jax-b/ModulerKTNE/Planing_Drawings/FrontOfDevice.JPG

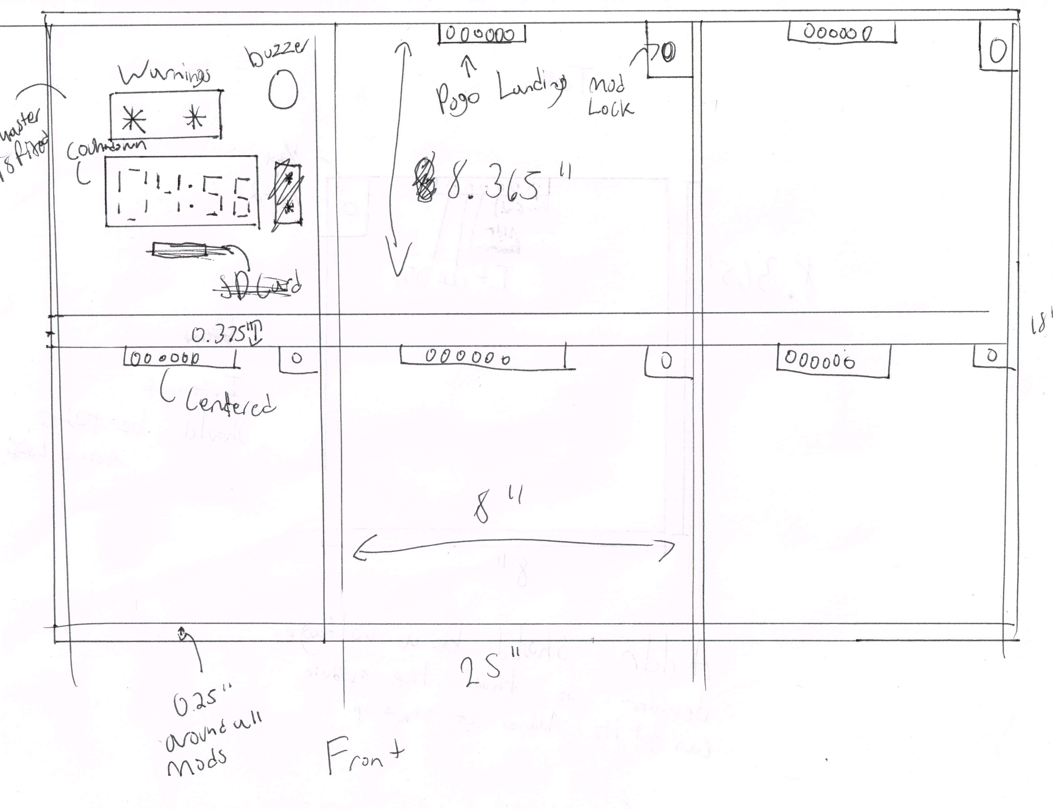
Planing_Drawings/FrontOfDevice.JPG
