jax-b/ModulerKTNE/Planing_Drawings/ModAddrs.JPG

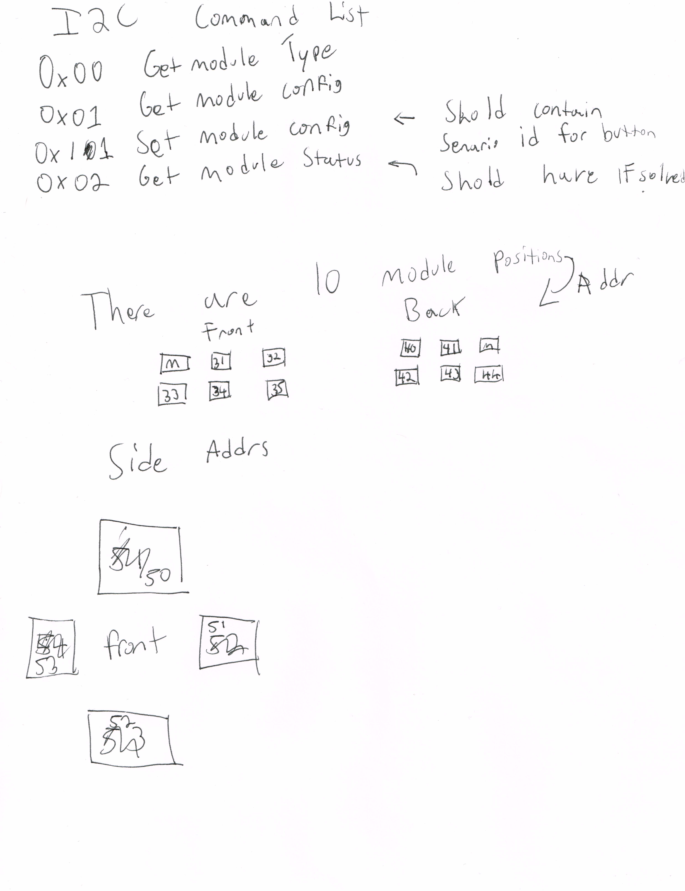
Planing_Drawings/ModAddrs.JPG
