jax-b/ModulerKTNE/Planing_Drawings/TheButton.JPG

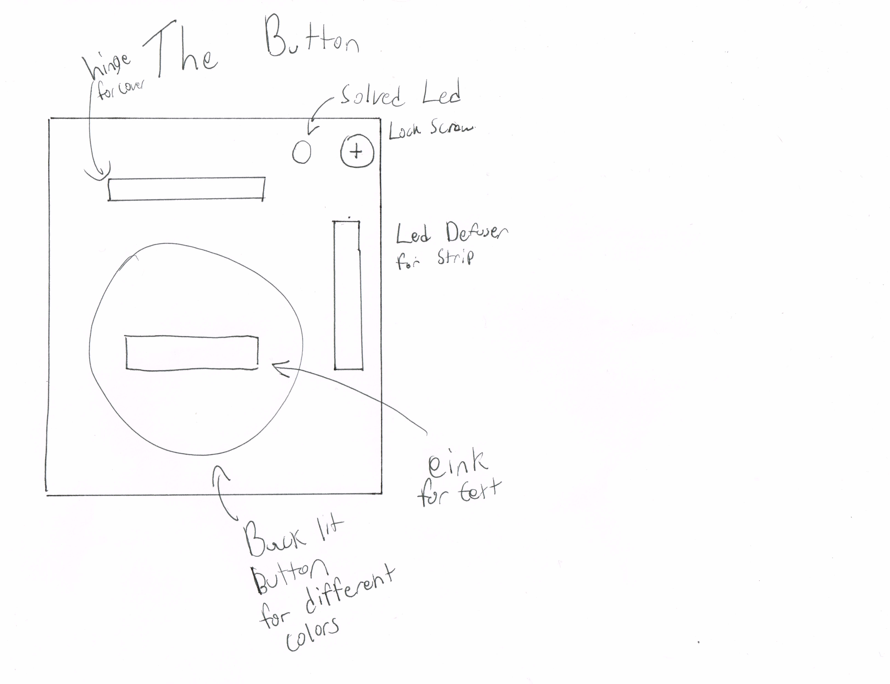
Planing_Drawings/TheButton.JPG
