jax-b/ModulerKTNE/SidePanel/Artwork/D.jpg

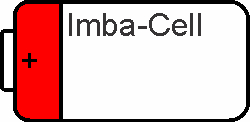
SidePanel/Artwork/D.jpg
