jax-b/ModulerKTNE/Modules/src/OTS_Wires/OTS_Wires Cut Buttons.3mf

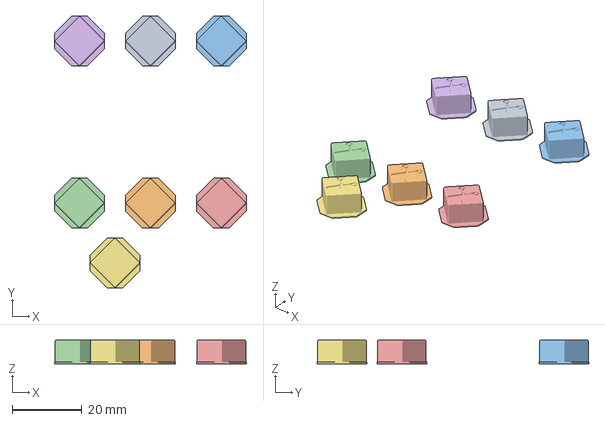
[picture p32: CAD file, 2022-03-22]
Modules/src/OTS_Wires/OTS_Wires Cut Buttons.3mf
55.1 x 78.1 x 6.86 mm
