jax-b/ModulerKTNE/SidePanel/LeftSideConductor/src/PortPictures.h

// Total bytes used to store images in PROGMEM = 6928
// 'rj45', 56x61px
const uint16_t epd_bitmap_rj45_size [] PROGMEM = { 56, 61 };
const unsigned char epd_bitmap_rj45_Black [] PROGMEM = {
	0x00, 0x00, 0x00, 0x00, 0x00, 0x00, 0x00, 0x7f, 0xff, 0xff, 0xff, 0xff, 0xff, 0xfe, 0x7f, 0xff, 
	0xff, 0xff, 0xff, 0xff, 0xfe, 0x7f, 0xff, 0xff, 0xff, 0xff, 0xff, 0xfe, 0x7f, 0xff, 0xff, 0xff, 
	0xff, 0xff, 0xfe, 0x7f, 0xff, 0xff, 0xff, 0xff, 0xff, 0xfe, 0x7f, 0xff, 0xff, 0xff, 0xff, 0xff, 
	0xfe, 0x7f, 0xff, 0xff, 0xff, 0xff, 0xff, 0xfe, 0x7f, 0xff, 0xff, 0xff, 0xff, 0xff, 0xfe, 0x7f, 
	0x00, 0x00, 0x00, 0x00, 0x00, 0x7e, 0x7f, 0x00, 0x00, 0x00, 0x00, 0x00, 0x7e, 0x7f, 0x00, 0x00, 
	0x00, 0x00, 0x00, 0x7e, 0x7f, 0x00, 0x00, 0x00, 0x00, 0x00, 0x7e, 0x7f, 0x00, 0x00, 0x00, 0x00, 
	0x00, 0x7e, 0x7f, 0x00, 0x00, 0x00, 0x00, 0x00, 0x7e, 0x7f, 0x00, 0x00, 0x00, 0x00, 0x00, 0x7e, 
	0x7f, 0x00, 0x00, 0x00, 0x00, 0x00, 0x7e, 0x7f, 0x00, 0x00, 0x00, 0x00, 0x00, 0x7e, 0x7f, 0x00, 
	0x00, 0x00, 0x00, 0x00, 0x7e, 0x7f, 0x00, 0x00, 0x00, 0x00, 0x00, 0x7e, 0x7f, 0x00, 0x00, 0x00, 
	0x00, 0x00, 0x7e, 0x7f, 0x00, 0x00, 0x00, 0x00, 0x00, 0x7e, 0x7f, 0x00, 0x00, 0x00, 0x00, 0x00, 
	0x7e, 0x7f, 0x00, 0x00, 0x00, 0x00, 0x00, 0x7e, 0x7f, 0x00, 0x00, 0x00, 0x00, 0x00, 0x7e, 0x7f, 
	0x00, 0x00, 0x00, 0x00, 0x00, 0x7e, 0x7f, 0x00, 0x00, 0x00, 0x00, 0x00, 0x7e, 0x7f, 0x00, 0x00, 
	0x00, 0x00, 0x00, 0x7e, 0x7f, 0x00, 0x00, 0x00, 0x00, 0x00, 0x7e, 0x7f, 0x00, 0x00, 0x00, 0x00, 
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
	0x01, 0xe0, 0x1e, 0x01, 0xe0, 0x1e, 0x1e, 0x1f, 0xff, 0xc0, 0x00, 0x3f, 0xe1, 0xc7, 0xff, 0x00, 
	0x1f, 0xfc, 0x78, 0x7f, 0xe3, 0xf0, 0x3f, 0x03, 0xf0, 0x3f, 0x03, 0xf0, 0x3f, 0x03, 0xf0, 0x3f, 
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
};
