jax-b/ModulerKTNE/Modules/src/OTS_Button/OTS_Button.h

#include "../baseModule/baseModule.h"
#include <Adafruit_NeoPixel.h>
#include <GxEPD2_BW.h>
#include <Fonts/FreeMonoBold12pt7b.h>

// To be changed bases off of selected microcontroller and pcb version
// Pins 32u4
#ifdef __AVR_ATmega32U4__
#define NEOPIXEL_PIN 10
#define BUTTON_PIN 7
#define EPD_CS 6
#define EPD_DC 5
#define EPD_BUSY A1
#endif

#ifdef ARDUINO_ARCH_RP2040
#define NEOPIXEL_PIN 21
#define BUTTON_PIN 7
#define EPD_CS 6
#define EPD_DC 5
#define EPD_BUSY A1
#endif

// Enable the timer in the main software loop
#define TIMER_ENABLE True

class OTS_Button : public baseModule
{
public:
    OTS_Button();
    // inherithed from baseModule
    virtual void setupModule();
    virtual void setSeed(uint16_t);
    virtual void tickModule(unsigned long);
    virtual void clearModule();

private:
    uint8_t buttonColor = 0x0;
    uint8_t stripColor = 0x0;
    uint32_t stripColorHex = 0x0;
    uint8_t chosenWord = 0x0; // index of the chosen word rather than having it be a whole character array. just makes things faster
    // only 4 possible words, placing them into an array then using the seed to choose which word will be displayed
    Adafruit_NeoPixel *_pixels;
    GxEPD2_BW<GxEPD2_154_D67, 32> _display = GxEPD2_154_D67(EPD_CS, EPD_DC, -1, EPD_BUSY);
    unsigned long timeLastBtn = 0;
    bool lastBTNState = 0;
    uint16_t textX = 0;
    uint16_t textY = 0;
    String strChosenWord = "";
    bool drawScreen = false;
    bool failureBTNReset = false;
    
protected:
    void relHeldButton(unsigned long);
    uint16_t btnDebounce();
};
